TomRBarber/BlueSCSI/docs/images/DB25Assembled.jpg

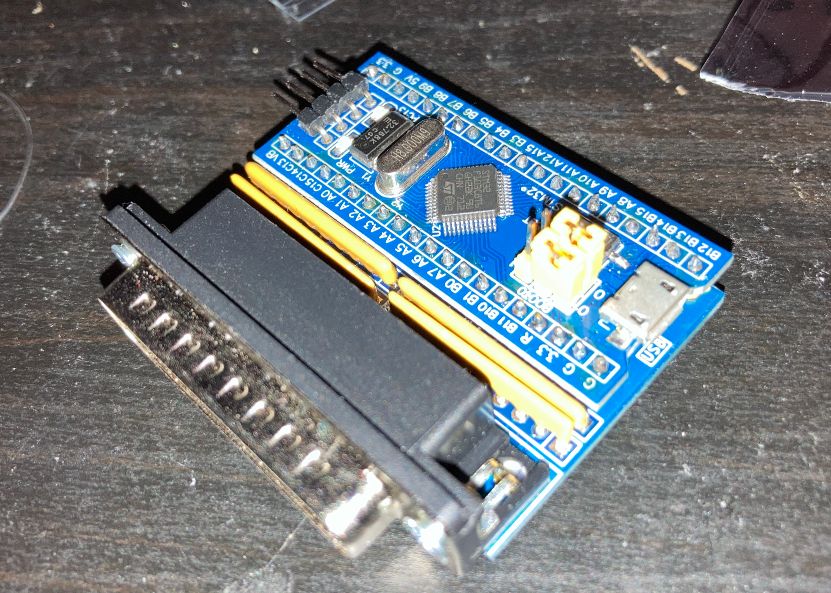
docs/images/DB25Assembled.jpg
