TomRBarber/BlueSCSI/docs/images/DesktopAssembled.jpg

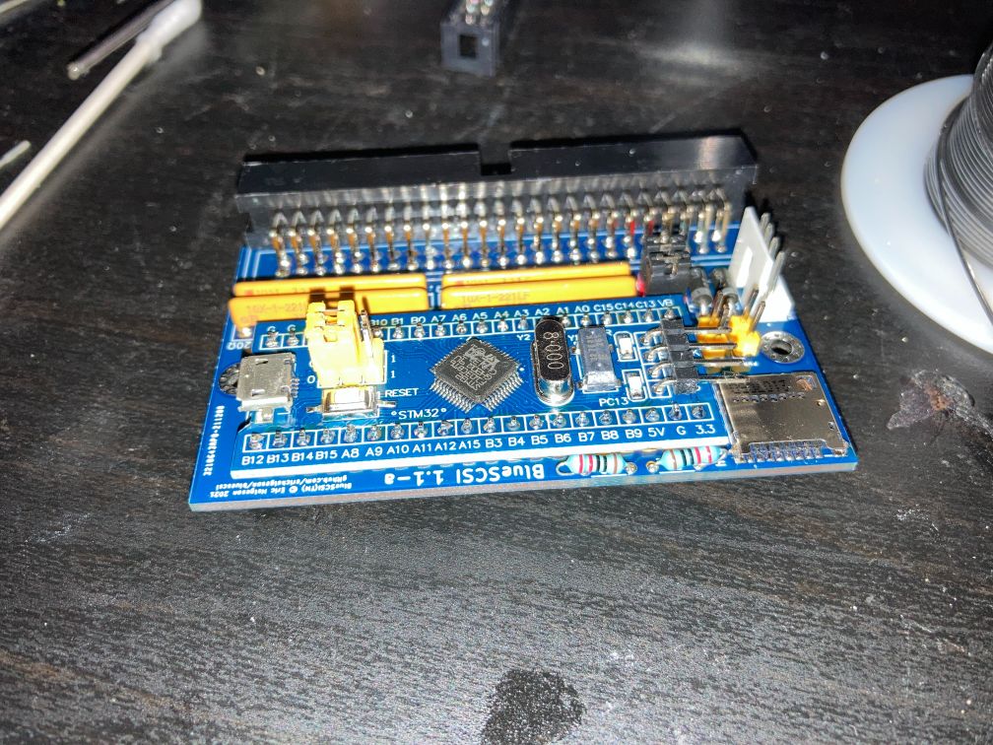
docs/images/DesktopAssembled.jpg
